KC-1857/impulsar-01/mechanical/impulsar-01-rev06/laser/kerf_coupon.dxf

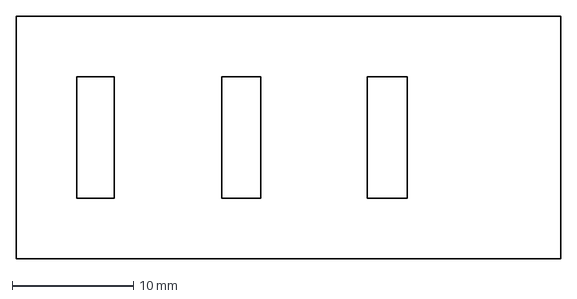
[picture p26: CAD file, 2026-09-30]
mechanical/impulsar-01-rev06/laser/kerf_coupon.dxf
45.0 x 20.0 mm
