KC-1857/impulsar-01/mechanical/impulsar-01-rev06/source/Corpus_paz_foot.stl

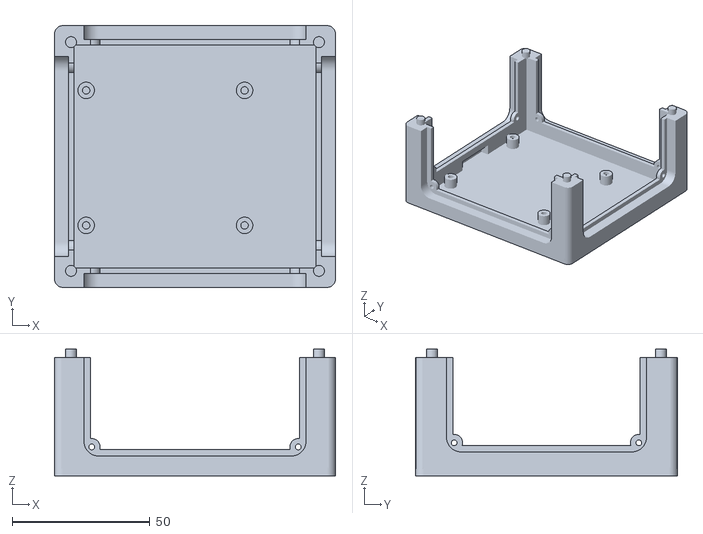
[picture p27: CAD file, 2026-09-24]
mechanical/impulsar-01-rev06/source/Corpus_paz_foot.stl
102.0 x 95.0 x 46.0
