KC-1857/impulsar-01/mechanical/Northern lights - 01/right.dxf

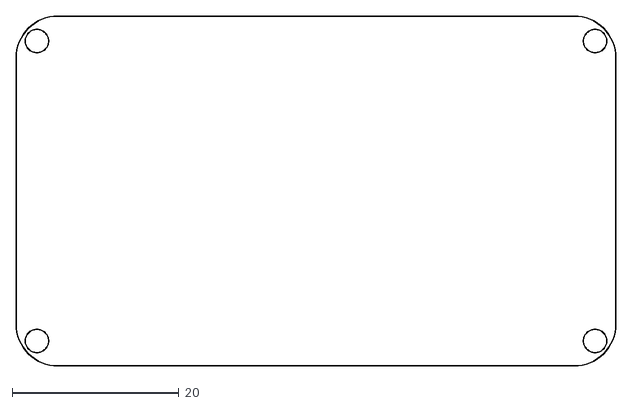
[picture p28: CAD file, 2026-09-24]
mechanical/Northern lights - 01/right.dxf
72.0 x 42.0
