KC-1857/impulsar-01/mechanical/impulsar-01-rev06/cad/step/front_acrylic.step

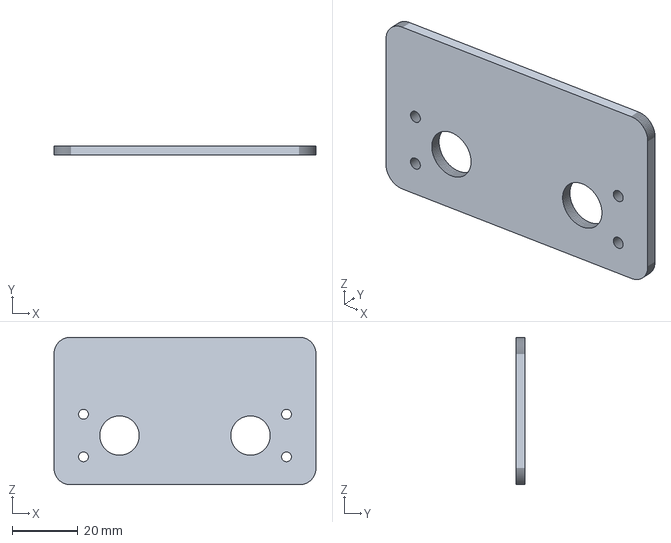
[picture p29: CAD file, 2026-09-30]
mechanical/impulsar-01-rev06/cad/step/front_acrylic.step
80.0 x 2.85 x 45.0 mm
