KC-1857/impulsar-01/mechanical/impulsar-01-rev06/laser/right_2p85.dxf

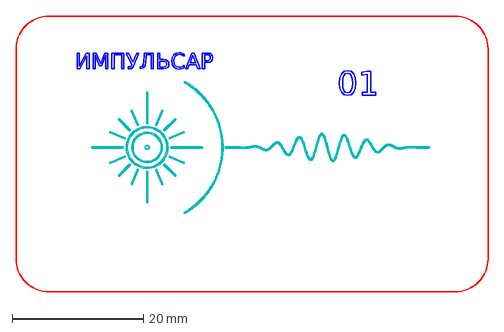
[picture p30: CAD file, 2026-09-30]
mechanical/impulsar-01-rev06/laser/right_2p85.dxf
72.0 x 42.0 mm
