KC-1857/impulsar-01/mechanical/Northern lights - 01/rear.dxf

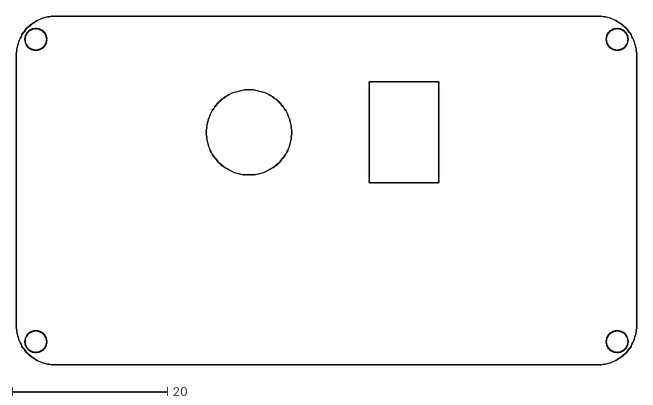
[picture p31: CAD file, 2026-09-24]
mechanical/Northern lights - 01/rear.dxf
80.0 x 45.0
