KC-1857/impulsar-01/mechanical/impulsar-01-rev06/cad/step/left_acrylic.step

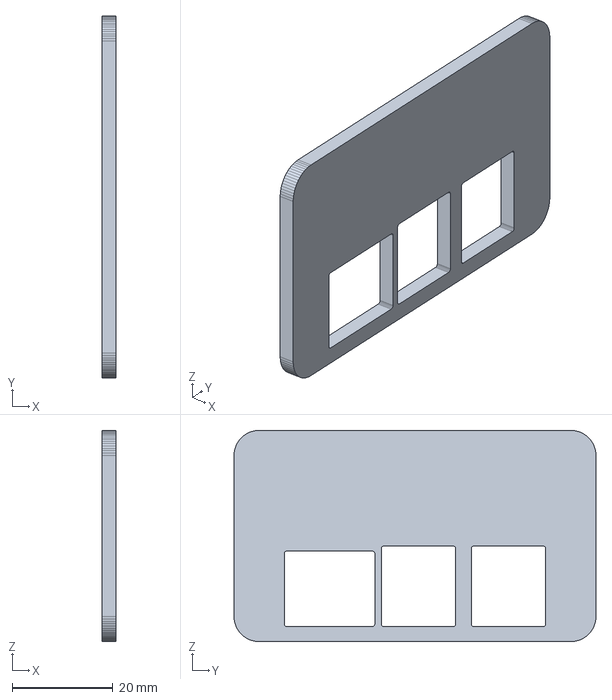
[picture p32: CAD file, 2026-09-30]
mechanical/impulsar-01-rev06/cad/step/left_acrylic.step
2.85 x 72.0 x 42.0 mm
