KC-1857/impulsar-01/mechanical/impulsar-01-rev06/coupons/actual_groove_print.stl

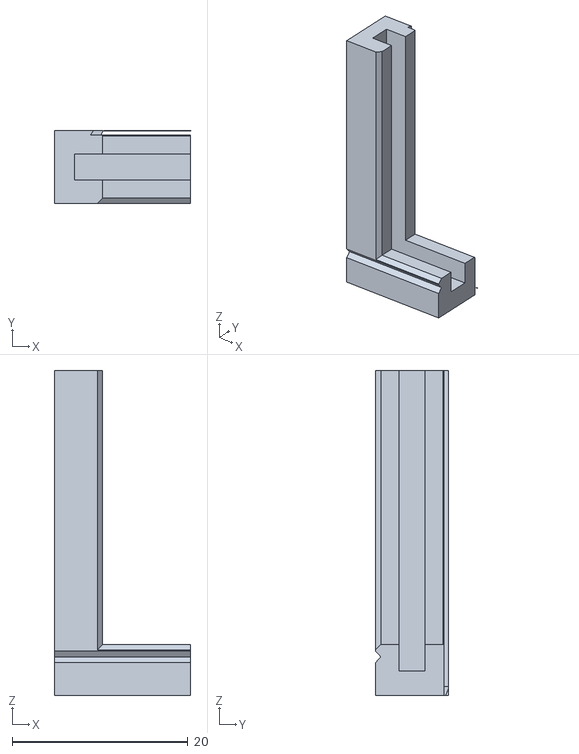
[picture p33: CAD file, 2026-09-30]
mechanical/impulsar-01-rev06/coupons/actual_groove_print.stl
15.5 x 8.31 x 37.0
