KC-1857/impulsar-01/mechanical/impulsar-01-rev06/laser/left_2p85.dxf

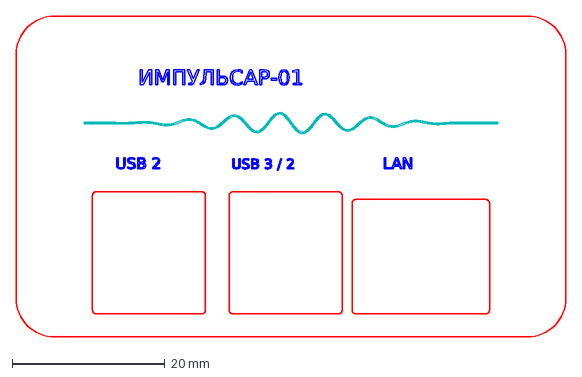
[picture p34: CAD file, 2026-09-30]
mechanical/impulsar-01-rev06/laser/left_2p85.dxf
72.0 x 42.0 mm
