KC-1857/impulsar-01/mechanical/Northern lights - 01/top.dxf

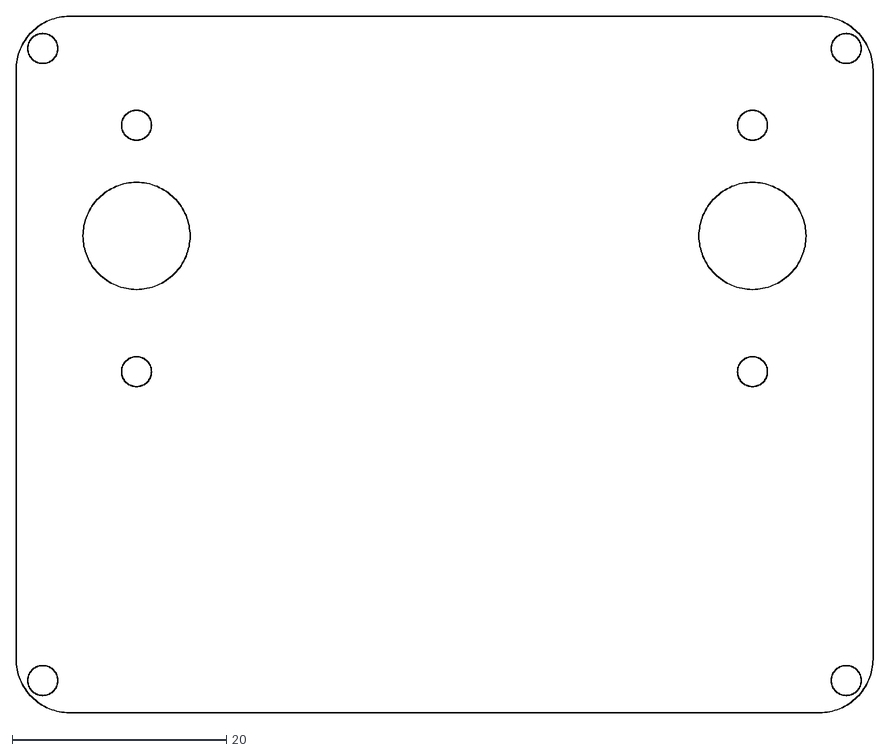
[picture p35: CAD file, 2026-09-24]
mechanical/Northern lights - 01/top.dxf
80.0 x 65.0
