KC-1857/impulsar-01/mechanical/impulsar-01-rev06/cad/step/right_acrylic.step

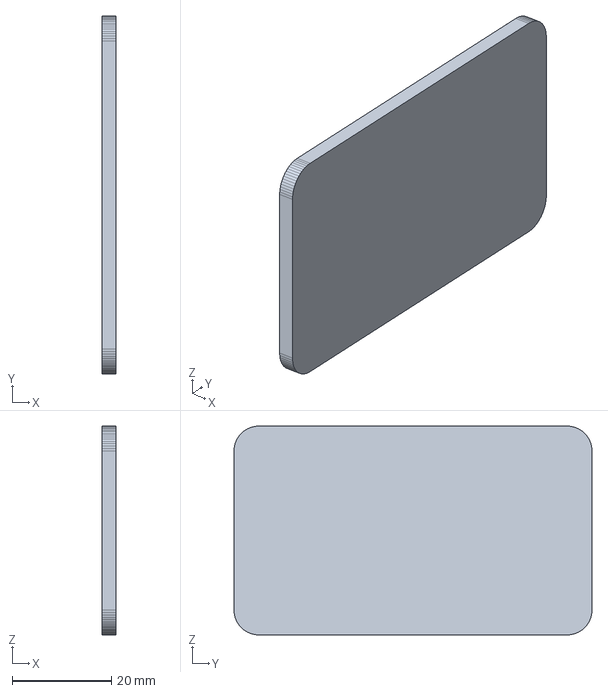
[picture p36: CAD file, 2026-09-30]
mechanical/impulsar-01-rev06/cad/step/right_acrylic.step
2.85 x 72.0 x 42.0 mm
