KC-1857/impulsar-01/mechanical/impulsar-01-rev06/laser/front_2p85.dxf

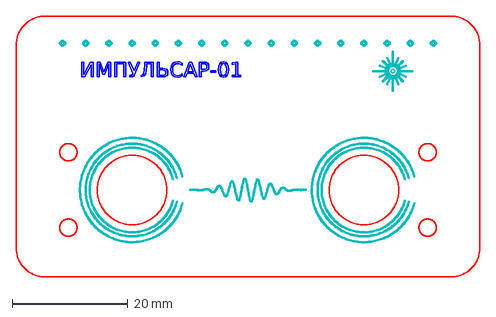
[picture p37: CAD file, 2026-09-30]
mechanical/impulsar-01-rev06/laser/front_2p85.dxf
80.0 x 45.0 mm
