KC-1857/impulsar-01/mechanical/impulsar-01-rev06/laser/engraving_coupon.dxf

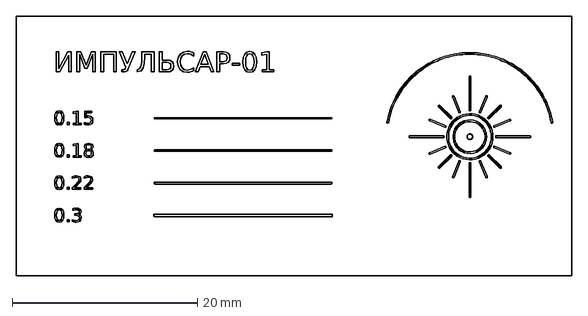
[picture p39: CAD file, 2026-09-30]
mechanical/impulsar-01-rev06/laser/engraving_coupon.dxf
60.0 x 28.0 mm
