KC-1857/impulsar-01/mechanical/impulsar-01-rev06/coupons/fixed_groove_print.stl

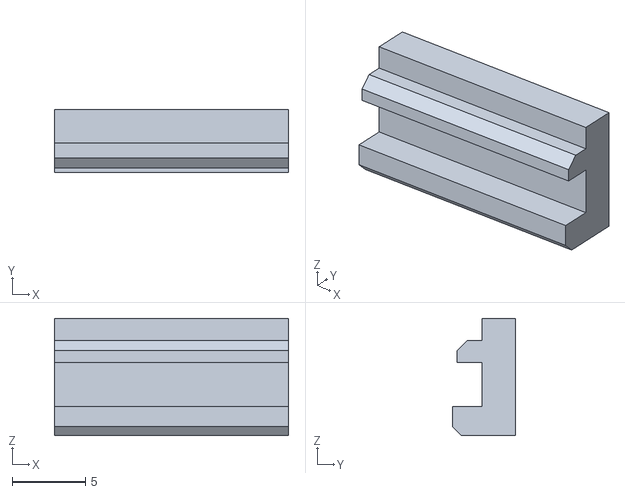
[picture p40: CAD file, 2026-09-30]
mechanical/impulsar-01-rev06/coupons/fixed_groove_print.stl
16.0 x 4.30 x 8.00
