KC-1857/impulsar-01/mechanical/impulsar-01-rev06/coupons/bar_mount_print.stl

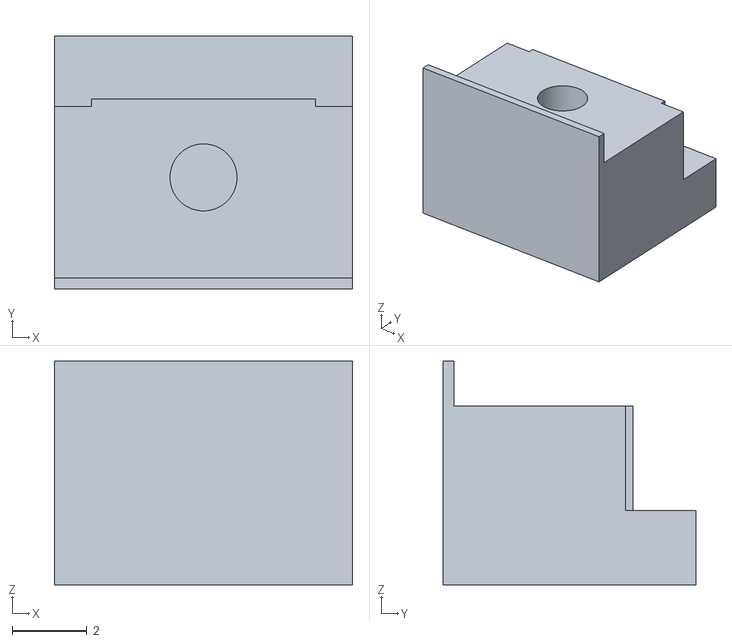
[picture p42: CAD file, 2026-09-30]
mechanical/impulsar-01-rev06/coupons/bar_mount_print.stl
8.00 x 6.80 x 6.00
