KC-1857/impulsar-01/mechanical/impulsar-01-rev06/coupons/groove_3.00_print.stl

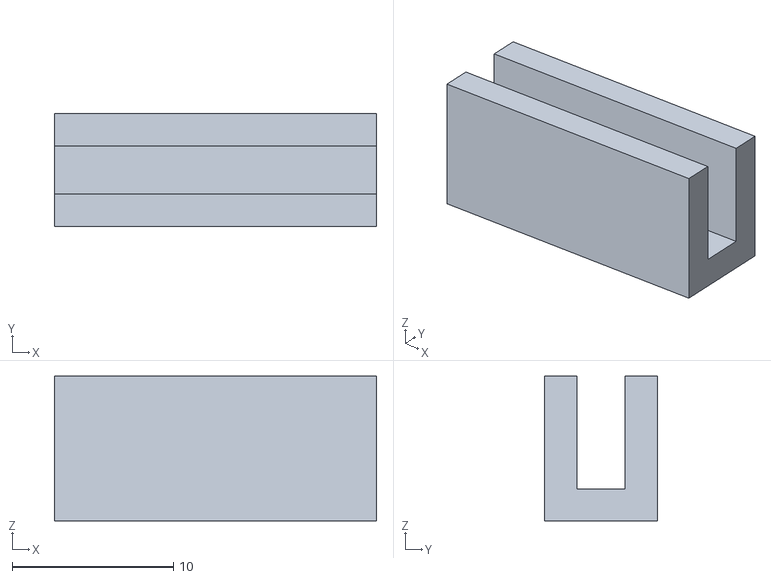
[picture p43: CAD file, 2026-09-30]
mechanical/impulsar-01-rev06/coupons/groove_3.00_print.stl
20.0 x 7.00 x 9.00
