KC-1857/impulsar-01/mechanical/impulsar-01-rev06/coupons/bar_end_print.stl

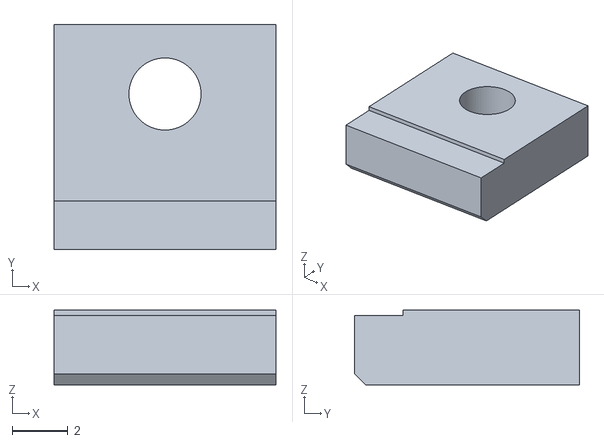
[picture p44: CAD file, 2026-09-30]
mechanical/impulsar-01-rev06/coupons/bar_end_print.stl
8.00 x 8.10 x 2.70
