KC-1857/impulsar-01/mechanical/impulsar-01-rev06/coupons/groove_2.95_print.stl

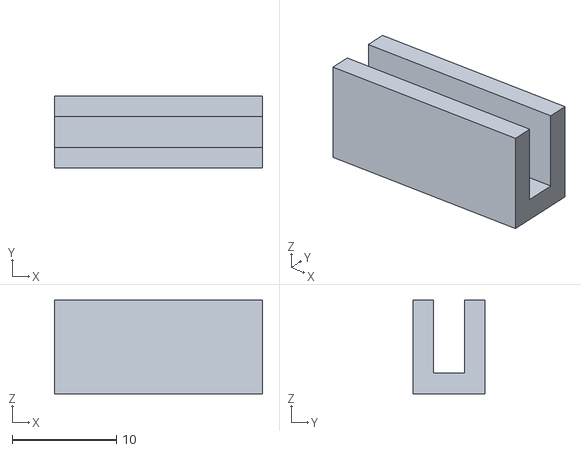
[picture p45: CAD file, 2026-09-30]
mechanical/impulsar-01-rev06/coupons/groove_2.95_print.stl
20.0 x 6.95 x 9.00
